wdouglass/pocket-reform/pocket-reform-charger/3d-models/21-0139I_T2444-4_MXM.step

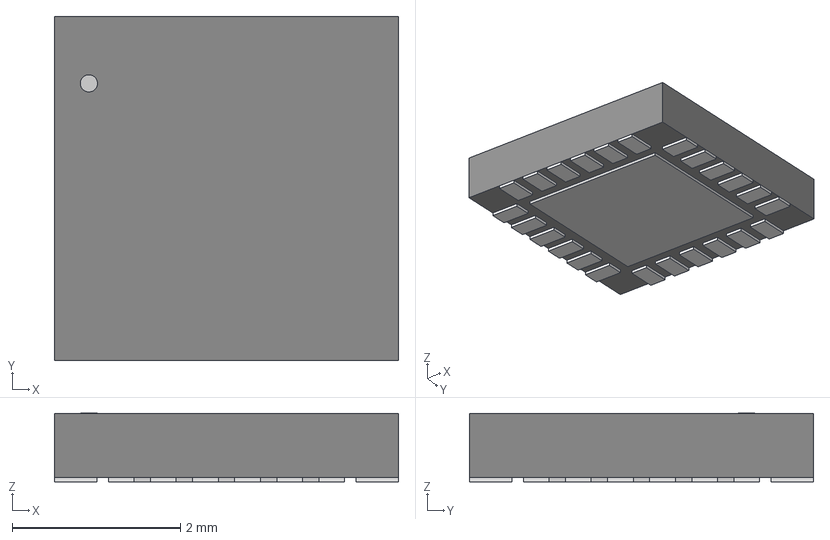
[picture p18: CAD file, 2023-04-12]
pocket-reform-charger/3d-models/21-0139I_T2444-4_MXM.step
4.09 x 4.09 x 0.815 mm
