wdouglass/pocket-reform/pocket-reform-headphones/3d-models/SR42W001.stp

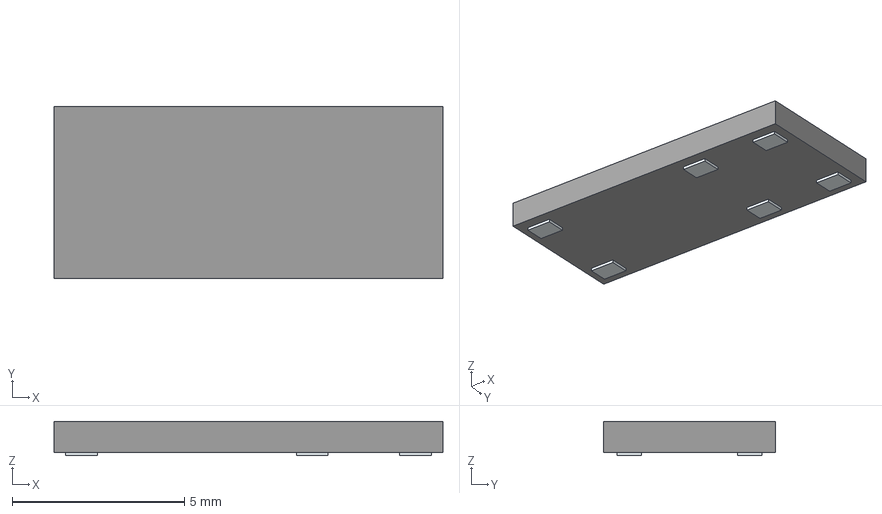
[picture p19: CAD file, 2024-01-16]
pocket-reform-headphones/3d-models/SR42W001.stp
11.3 x 5.00 x 1.00 mm
Pins
