wdouglass/pocket-reform/pocket-reform-motherboard/3d-models/SM02B-SRSS-TB-LF--SN---3DModel-STEP-56544.STEP

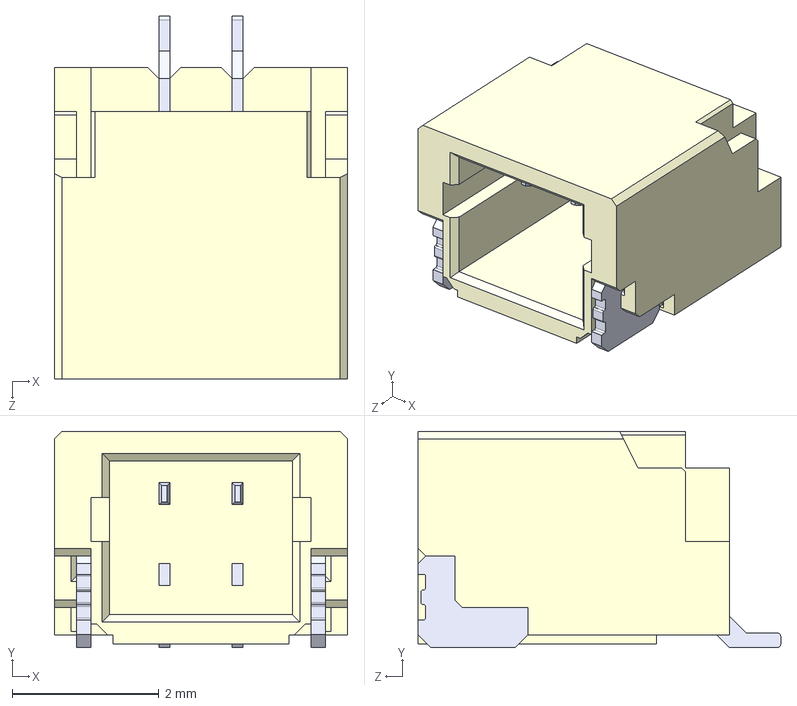
[picture p20: CAD file, 2023-11-24]
pocket-reform-motherboard/3d-models/SM02B-SRSS-TB-LF--SN---3DModel-STEP-56544.STEP
4.00 x 2.95 x 4.95 mm
