wdouglass/pocket-reform/attic/pocket-reform-keyboard/3d-models/Cherry_-_ML1A-11NW.step

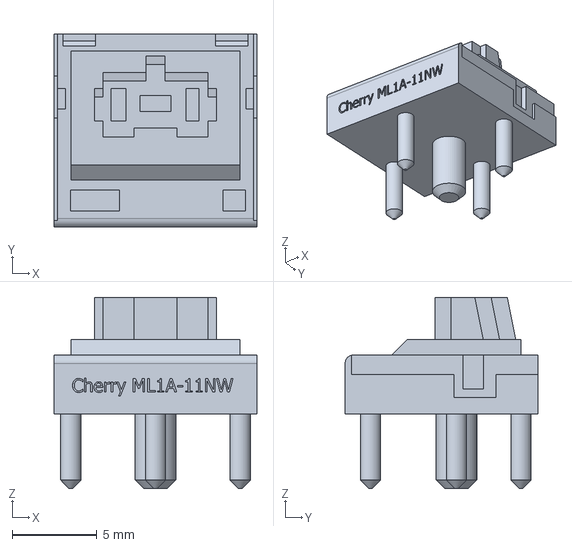
[picture p21: CAD file, 2021-04-30]
attic/pocket-reform-keyboard/3d-models/Cherry_-_ML1A-11NW.step
12.0 x 11.4 x 11.3 mm
