wdouglass/pocket-reform/pocket-reform-charger/3d-models/S9B-PH-SM4-TB.stp

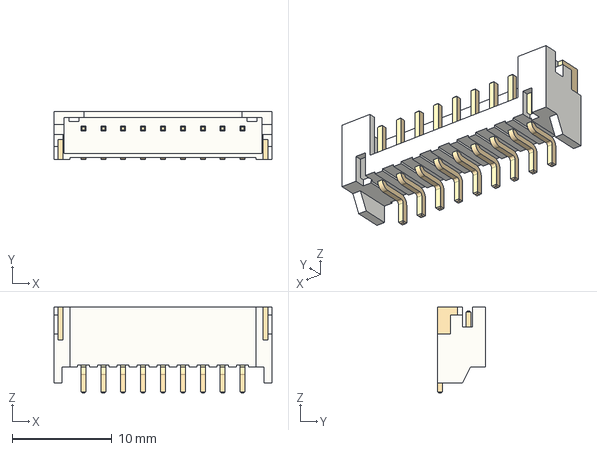
[picture p22: CAD file, 2022-06-08]
pocket-reform-charger/3d-models/S9B-PH-SM4-TB.stp
21.9 x 4.80 x 8.60 mm
