wdouglass/pocket-reform/pocket-reform-headphones/3d-models/SM05B-SRSS-TB(LF)(SN)--3DModel-STEP-418109.STEP

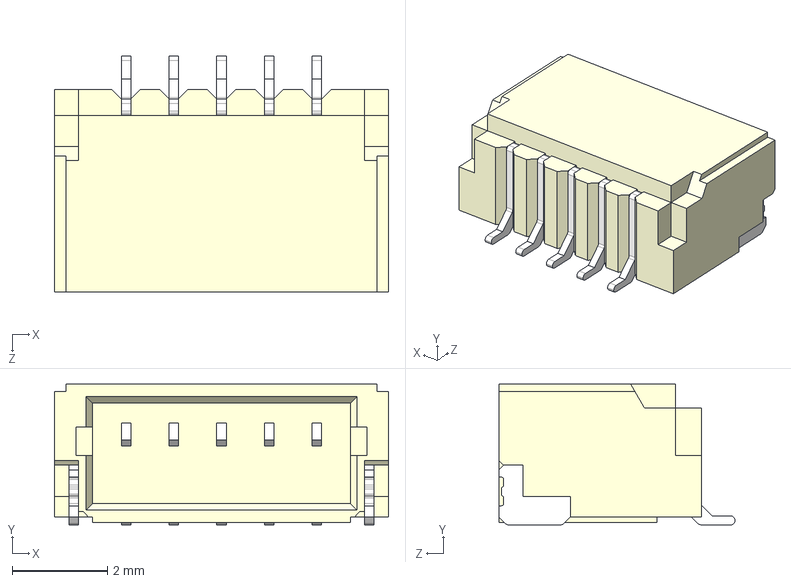
[picture p23: CAD file, 2023-09-29]
pocket-reform-headphones/3d-models/SM05B-SRSS-TB(LF)(SN)--3DModel-STEP-418109.STEP
7.00 x 2.95 x 4.95 mm
