wdouglass/pocket-reform/pocket-reform-headphones/3d-models/CUI_SJ-43516-SMT-TR.step

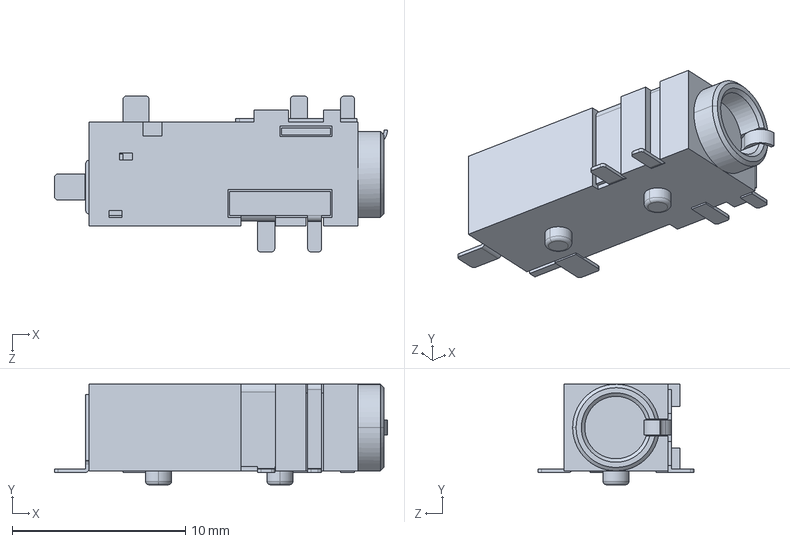
[picture p24: CAD file, 2021-07-28]
pocket-reform-headphones/3d-models/CUI_SJ-43516-SMT-TR.step
19.2 x 5.80 x 9.00 mm
