wdouglass/pocket-reform/pocket-reform-motherboard/3d-models/TSM-103-01-L-DH.step

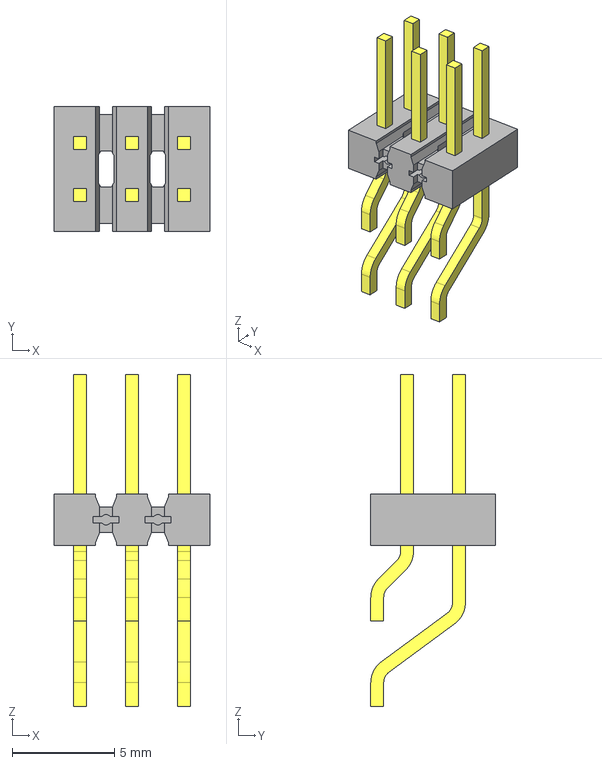
[picture p26: CAD file, 2023-08-25]
pocket-reform-motherboard/3d-models/TSM-103-01-L-DH.step
7.62 x 6.10 x 16.3 mm
T-1S6-09(-01-3-DH)
TSM-103-01-DH_body
