wdouglass/pocket-reform/pocket-reform-motherboard/3d-models/3215-crystal.step

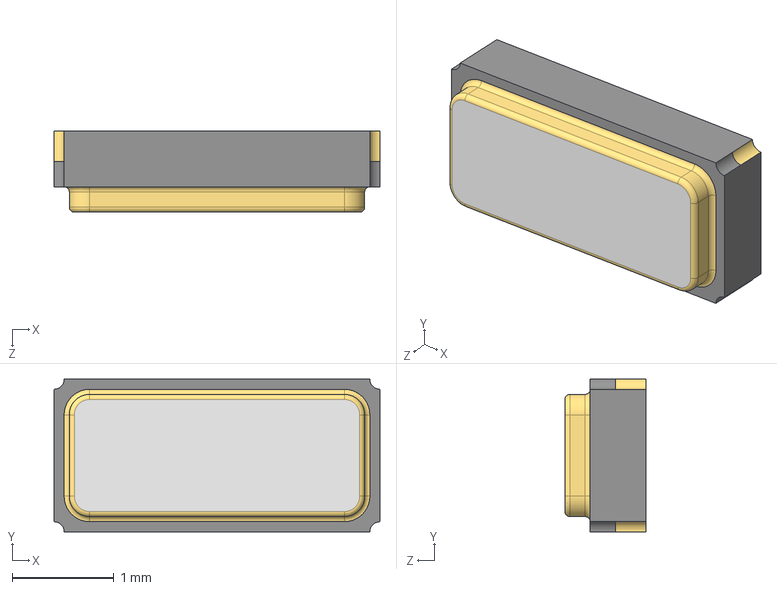
[picture p27: CAD file, 2022-06-17]
pocket-reform-motherboard/3d-models/3215-crystal.step
3.20 x 1.50 x 0.8 mm
