wdouglass/pocket-reform/pocket-reform-motherboard/3d-models/HTQFP-80.stp

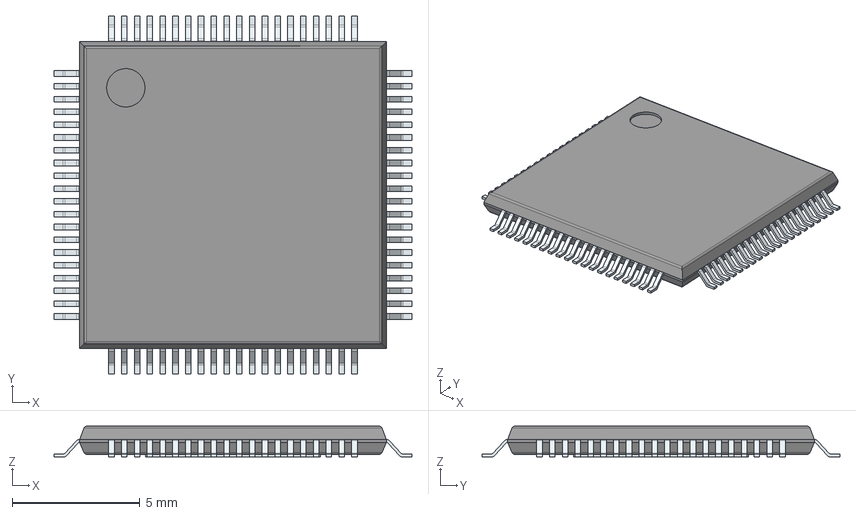
[picture p28: CAD file, 2022-06-17]
pocket-reform-motherboard/3d-models/HTQFP-80.stp
14.0 x 14.0 x 1.20 mm
PinsArrayLR
PinsArrayTB
ThermalPad
