wdouglass/pocket-reform/pocket-reform-motherboard/3d-models/SOD-128.step

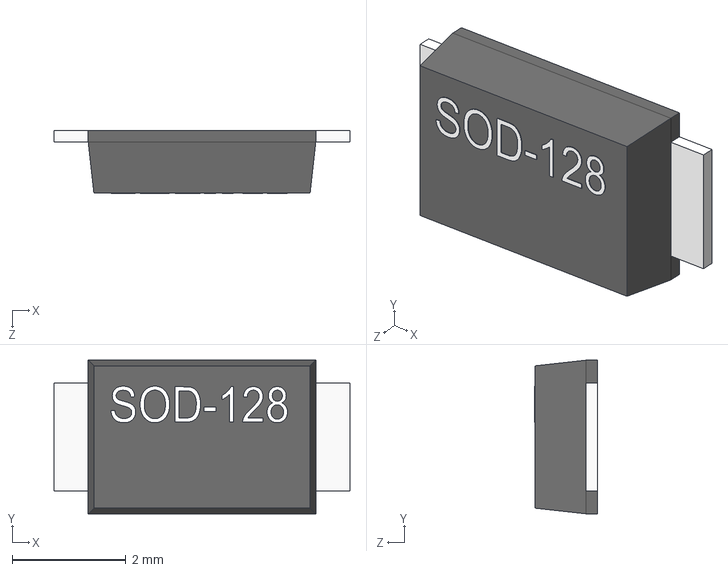
[picture p29: CAD file, 2022-06-17]
pocket-reform-motherboard/3d-models/SOD-128.step
5.20 x 2.70 x 1.11 mm
