wdouglass/pocket-reform/pocket-reform-motherboard/3d-models/IHLP4040DZ (2.2-100uH).STEP

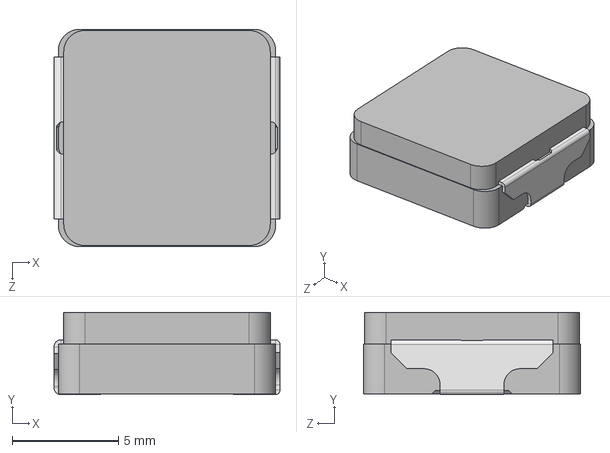
[picture p30: CAD file, 2022-06-08]
pocket-reform-motherboard/3d-models/IHLP4040DZ (2.2-100uH).STEP
10.6 x 3.87 x 10.2 mm
