wdouglass/pocket-reform/pocket-reform-motherboard/3d-models/BK-879.STEP

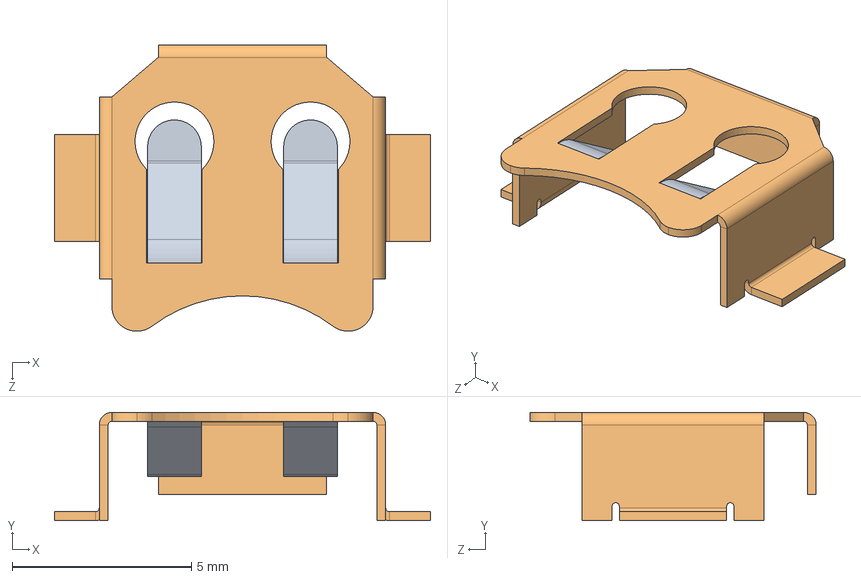
[picture p31: CAD file, 2022-06-08]
pocket-reform-motherboard/3d-models/BK-879.STEP
10.5 x 3.02 x 8.00 mm
