wdouglass/pocket-reform/pocket-reform-motherboard/3d-models/TLV320AIC3100IRHBR.STEP

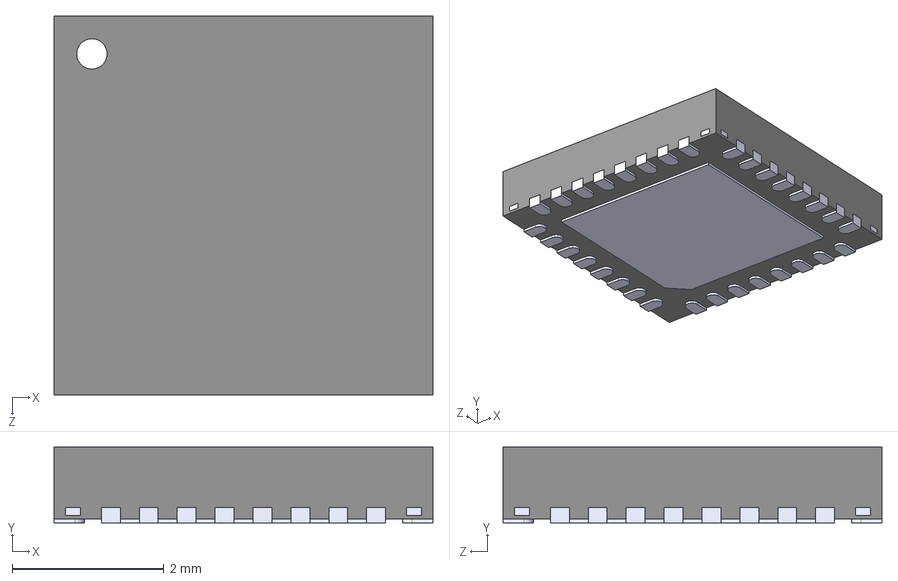
[picture p32: CAD file, 2022-06-08]
pocket-reform-motherboard/3d-models/TLV320AIC3100IRHBR.STEP
5.00 x 1.00 x 5.00 mm
