wdouglass/pocket-reform/pocket-reform-motherboard/3d-models/FH12-33S-0.5SH.stp

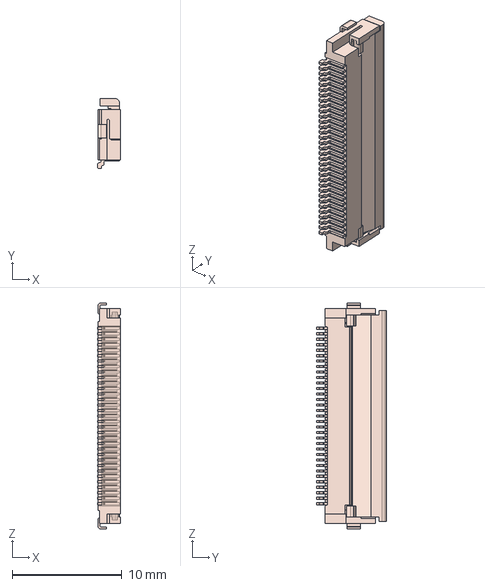
[picture p33: CAD file, 2022-06-08]
pocket-reform-motherboard/3d-models/FH12-33S-0.5SH.stp
2.10 x 6.40 x 20.6 mm
