wdouglass/pocket-reform/pocket-reform-motherboard/3d-models/ssfv33r_1stlf.stp

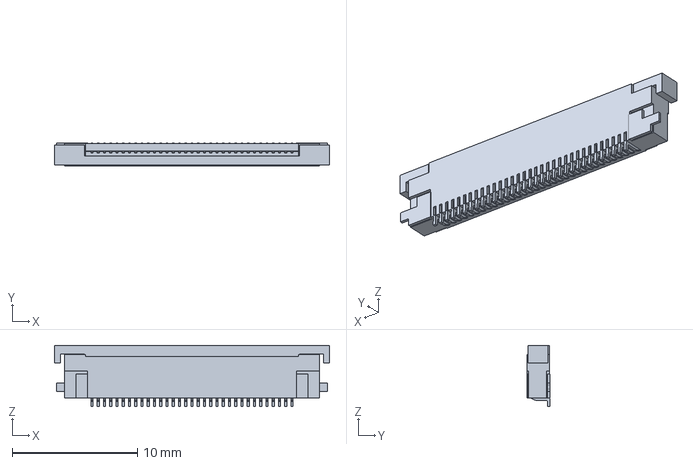
[picture p35: CAD file, 2022-06-08]
pocket-reform-motherboard/3d-models/ssfv33r_1stlf.stp
22.0 x 1.87 x 4.90 mm
