wdouglass/pocket-reform/pocket-reform-motherboard/3d-models/19-337-R6GHBHC-A01-2T.STEP

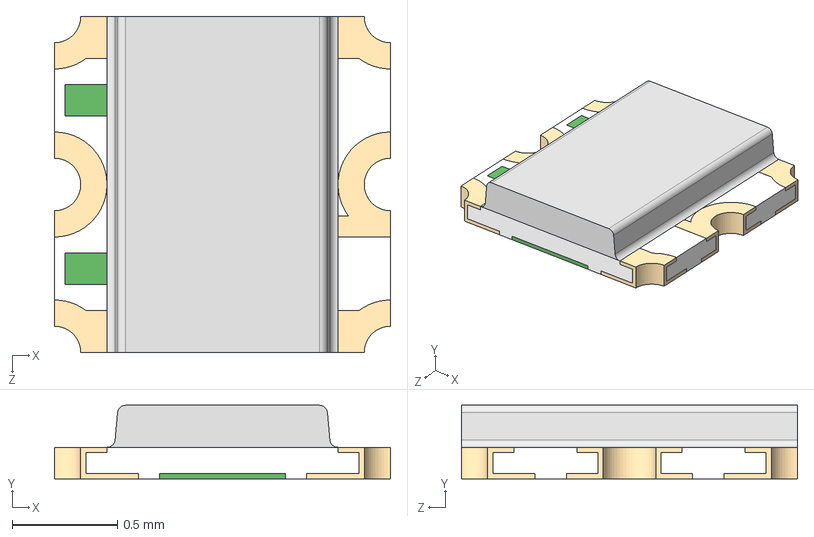
[picture p36: CAD file, 2022-06-08]
pocket-reform-motherboard/3d-models/19-337-R6GHBHC-A01-2T.STEP
1.60 x 0.35 x 1.60 mm
