wdouglass/pocket-reform/pocket-reform-motherboard/3d-models/TYPE-C-31-M-12--3DModel-STEP-56544.STEP

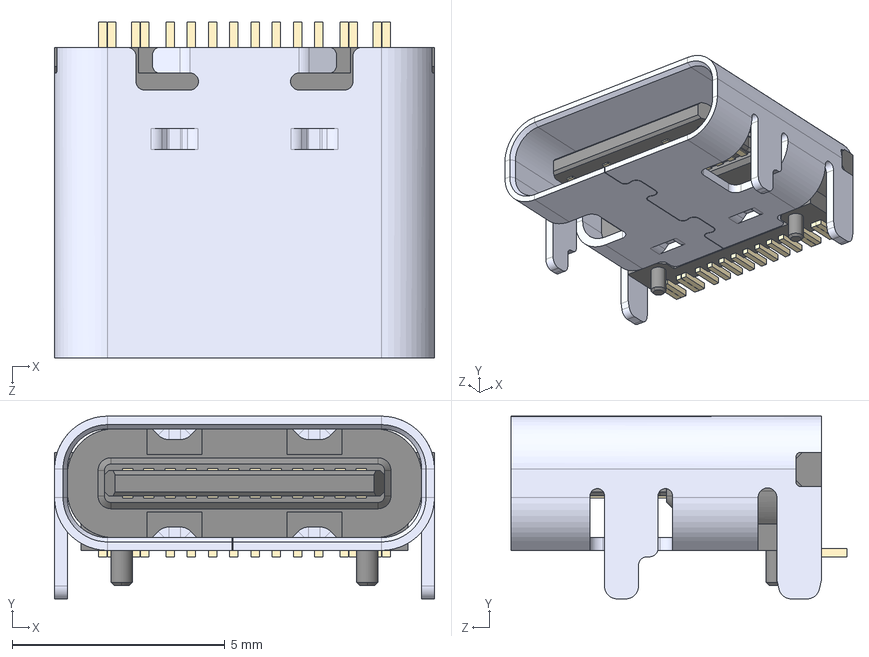
[picture p37: CAD file, 2022-06-08]
pocket-reform-motherboard/3d-models/TYPE-C-31-M-12--3DModel-STEP-56544.STEP
8.94 x 4.30 x 7.90 mm
