wdouglass/pocket-reform/pocket-reform-motherboard/3d-models/IND_TAIYO_NRH3012_TAY.step

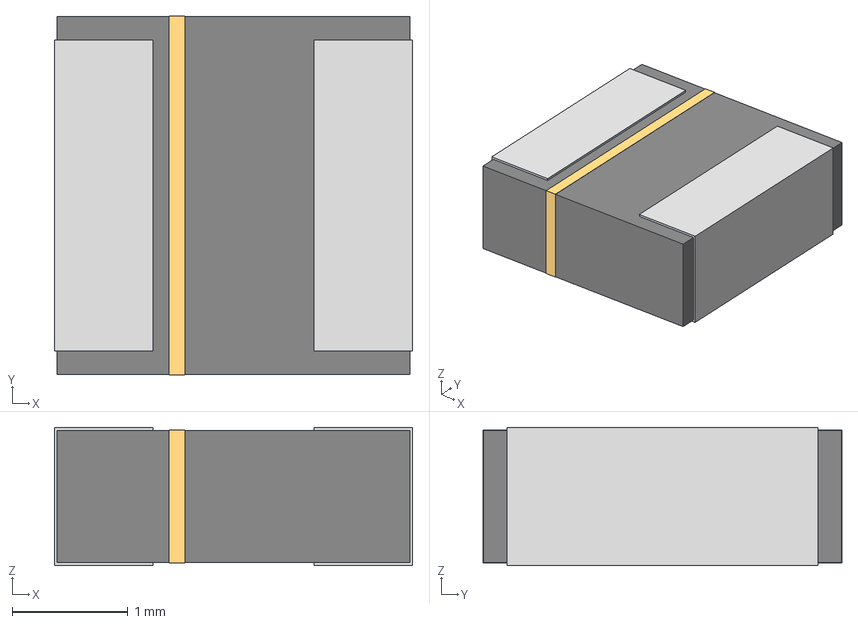
[picture p38: CAD file, 2022-06-08]
pocket-reform-motherboard/3d-models/IND_TAIYO_NRH3012_TAY.step
3.10 x 3.10 x 1.19 mm
