wdouglass/pocket-reform/pocket-reform-motherboard/3d-models/DM3AT-SF-PEJM5--3DModel-STEP-56544.STEP

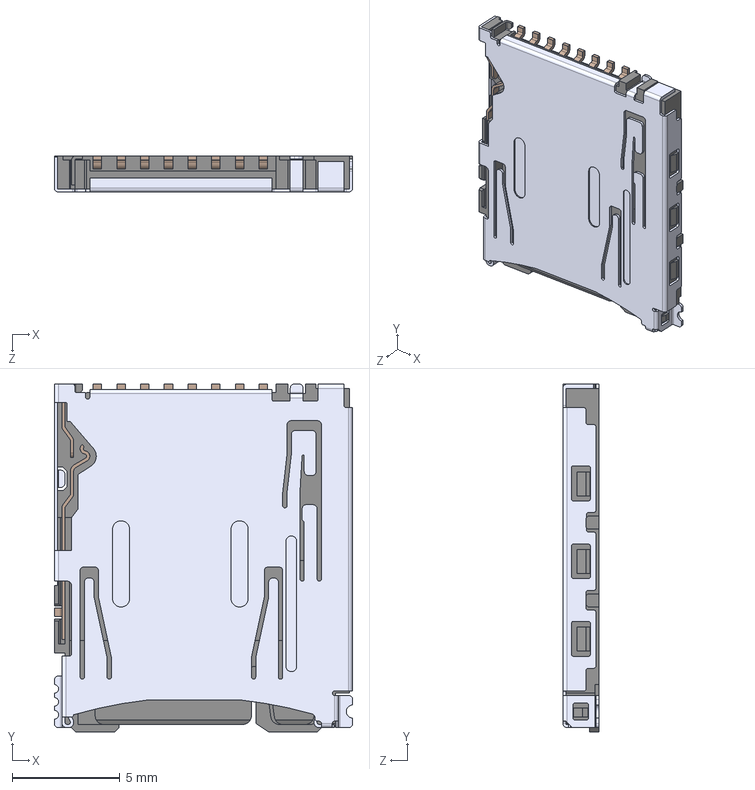
[picture p39: CAD file, 2022-06-08]
pocket-reform-motherboard/3d-models/DM3AT-SF-PEJM5--3DModel-STEP-56544.STEP
13.8 x 16.2 x 1.68 mm
