wdouglass/pocket-reform/pocket-reform-motherboard/3d-models/CM2020-00TR--3DModel-STEP-56544.STEP

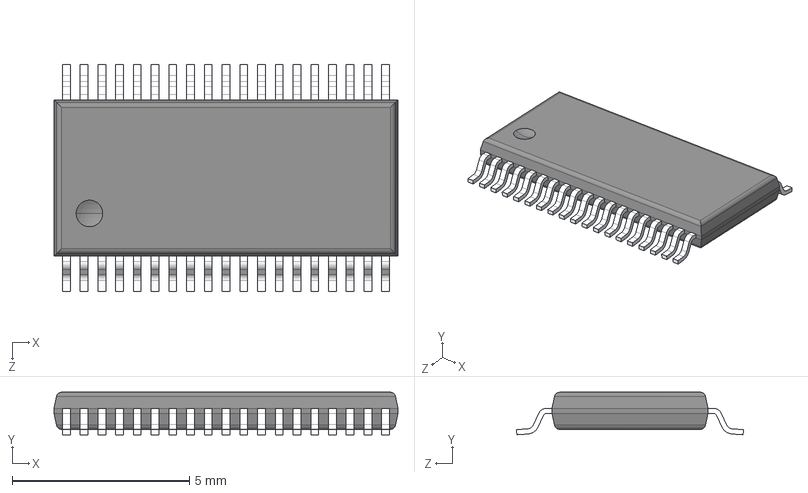
[picture p40: CAD file, 2022-06-08]
pocket-reform-motherboard/3d-models/CM2020-00TR--3DModel-STEP-56544.STEP
9.70 x 1.20 x 6.40 mm
