wdouglass/pocket-reform/pocket-reform-motherboard/3d-models/3-2328724-1.step

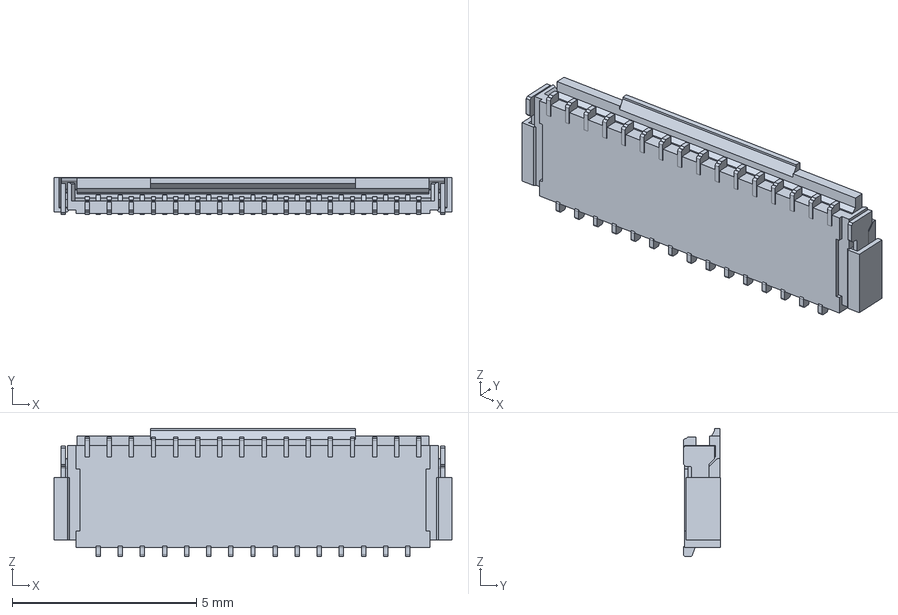
[picture p41: CAD file, 2022-05-31]
pocket-reform-motherboard/3d-models/3-2328724-1.step
10.8 x 1.00 x 3.48 mm
