wdouglass/pocket-reform/pocket-reform-motherboard/3d-models/c-1-2199230-5-b2-3d.stp

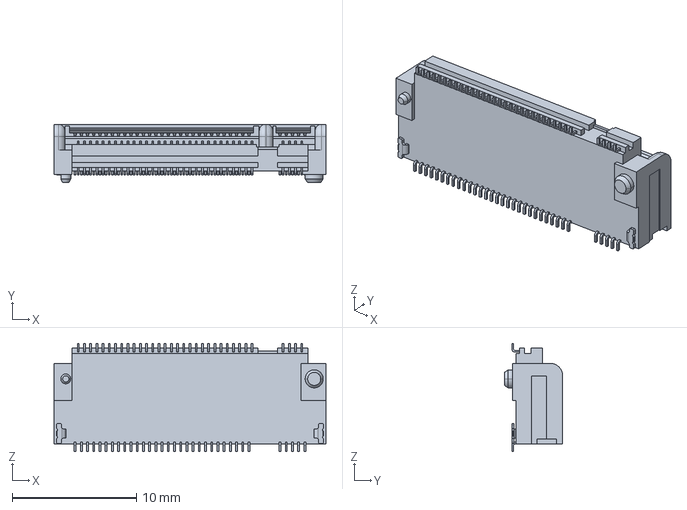
[picture p42: CAD file, 2022-05-31]
pocket-reform-motherboard/3d-models/c-1-2199230-5-b2-3d.stp
21.9 x 4.70 x 8.70 mm
