wdouglass/pocket-reform/pocket-reform-motherboard/3d-models/SON95P300X300X80-7N.step

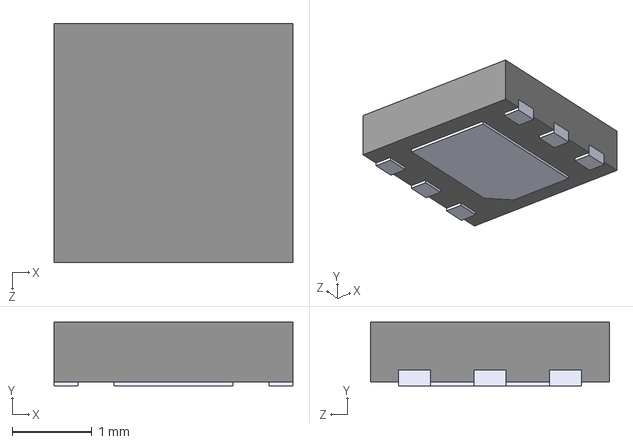
[picture p43: CAD file, 2022-05-31]
pocket-reform-motherboard/3d-models/SON95P300X300X80-7N.step
3.00 x 0.8 x 3.00 mm
