wdouglass/pocket-reform/pocket-reform-motherboard/3d-models/wuerth_692121030100_usb3.stp

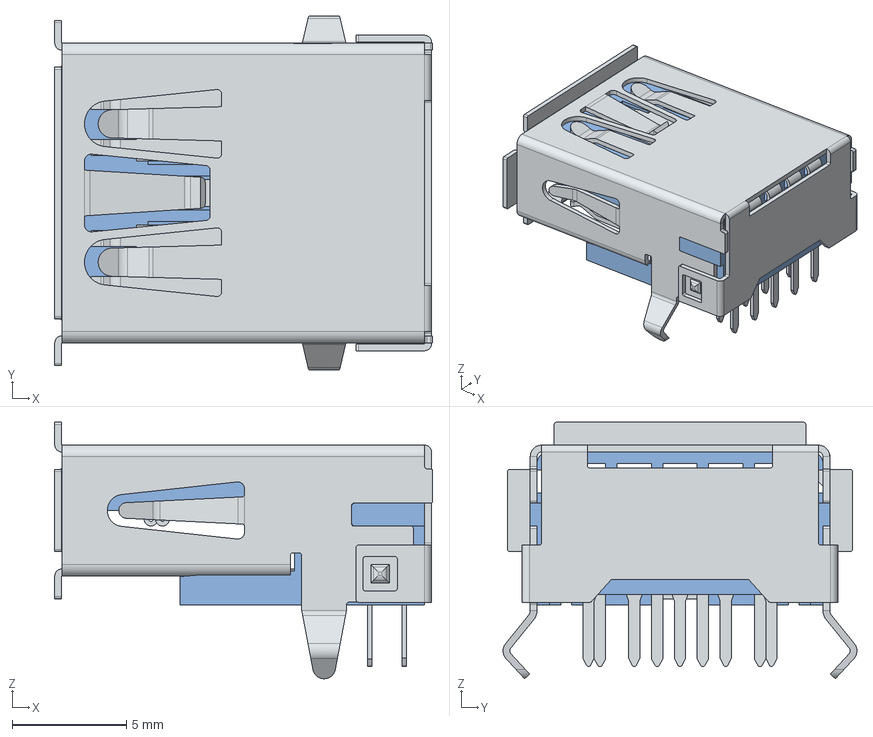
[picture p44: CAD file, 2022-05-31]
pocket-reform-motherboard/3d-models/wuerth_692121030100_usb3.stp
16.6 x 15.5 x 11.2 mm
housing1
pin1 x 5
housing2
pin2 x 2
pin x 2
shielding
