wdouglass/pocket-reform/pocket-reform-motherboard/3d-models/p36-2.stp

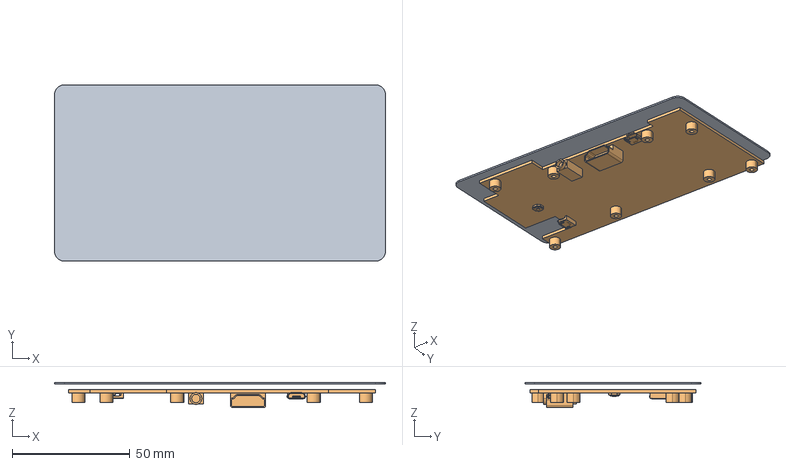
[picture p45: CAD file, 2021-07-28]
pocket-reform-motherboard/3d-models/p36-2.stp
140.4 x 74.8 x 10.8 mm
