wdouglass/pocket-reform/pocket-reform-motherboard/3d-models/Bateria 18650 3.7 V 1300 mAh d.18 mm.STEP

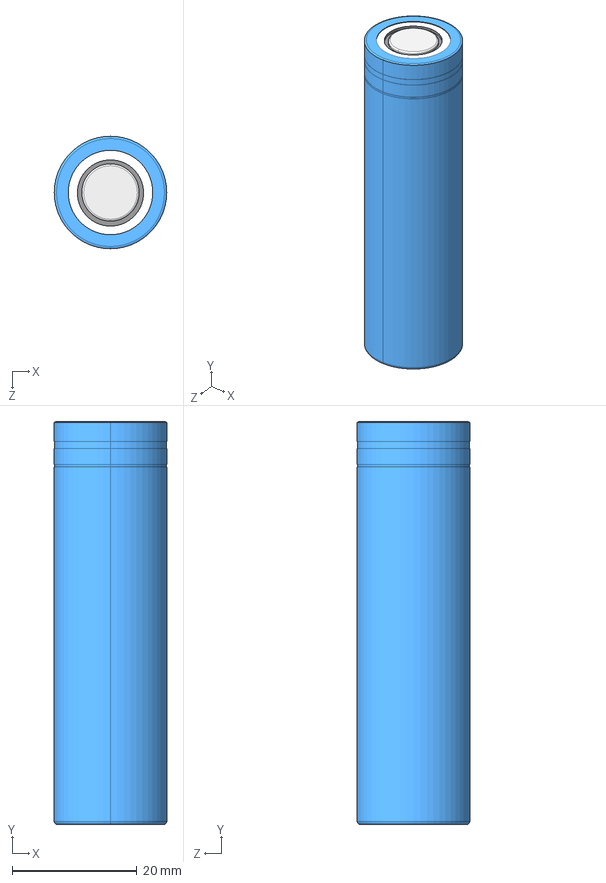
[picture p46: CAD file, 2021-07-28]
pocket-reform-motherboard/3d-models/Bateria 18650 3.7 V 1300 mAh d.18 mm.STEP
18.1 x 64.7 x 18.1 mm
