wdouglass/pocket-reform/pocket-reform-motherboard/3d-models/DM3CS-SFb.stp

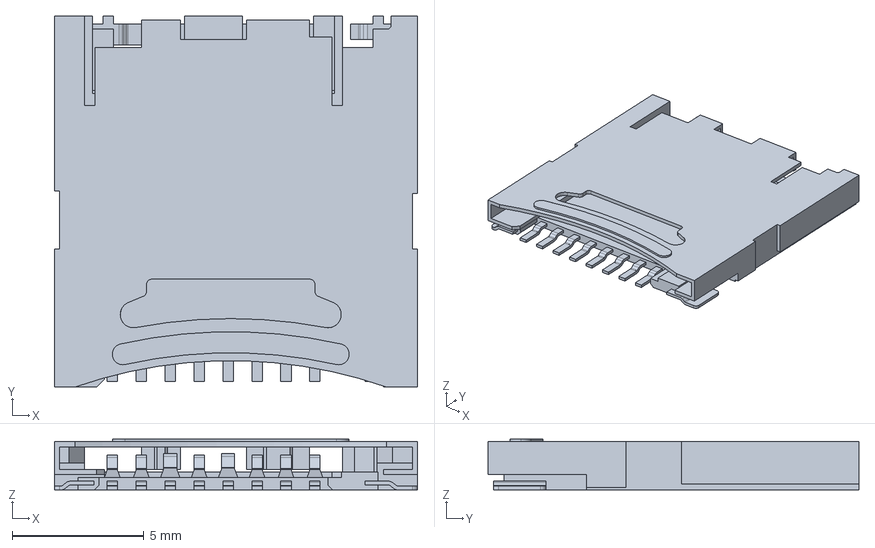
[picture p47: CAD file, 2021-07-28]
pocket-reform-motherboard/3d-models/DM3CS-SFb.stp
13.8 x 14.1 x 1.93 mm
