wdouglass/pocket-reform/pocket-reform-motherboard/3d-models/keystone-PN54.STEP

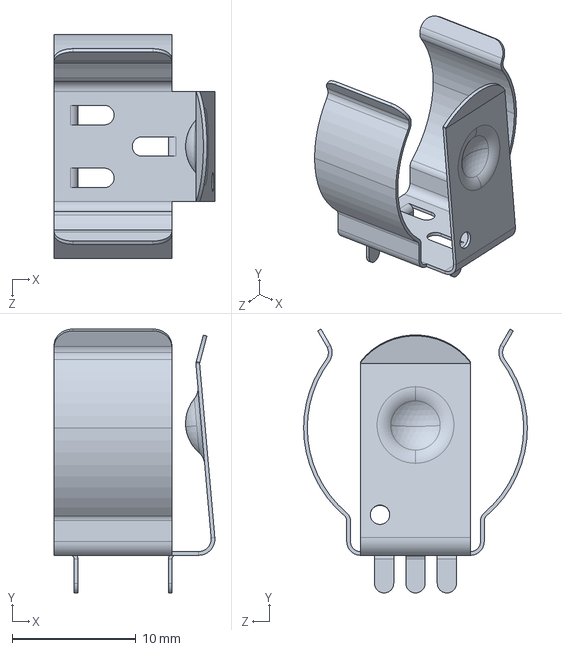
[picture p48: CAD file, 2021-07-28]
pocket-reform-motherboard/3d-models/keystone-PN54.STEP
13.0 x 21.4 x 18.1 mm
