wdouglass/pocket-reform/pocket-reform-motherboard/3d-models/c-2199337-5-a-3d.stp

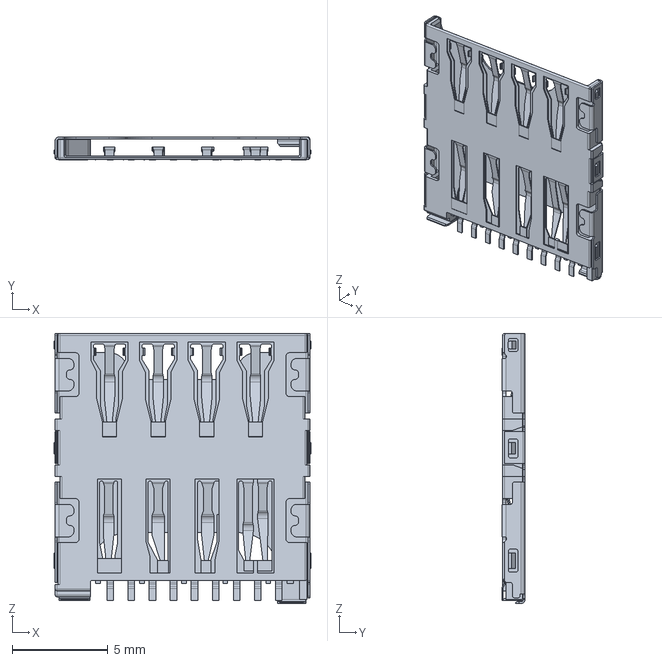
[picture p49: CAD file, 2021-07-28]
pocket-reform-motherboard/3d-models/c-2199337-5-a-3d.stp
13.4 x 1.20 x 14.1 mm
