wdouglass/pocket-reform/pocket-reform-keyboard-fw/pocket-hid/src/remote.h

/*
  SPDX-License-Identifier: GPL-3.0-or-later
  MNT Pocket Reform Keyboard/Trackball Controller Firmware for RP2040
  Copyright 2021-2024 MNT Research GmbH (mntre.com)
*/

#ifndef _REMOTE_H_
#define _REMOTE_H_

void insert_bat_icon(char* str, int x, double v);
void empty_serial(void);
int remote_receive_string(int print);
int remote_try_wakeup(void);
int remote_try_command(const char* cmd, int print_response);
int remote_get_voltages(int quiet);
int remote_check_for_low_battery(void);
int remote_get_status(void);
int remote_turn_on_som(void);
int remote_turn_off_som(void);
int remote_reset_som(void);
int remote_wake_som(void);
int remote_report_voltages(void);
int remote_enable_som_uart(void);
int remote_disable_som_uart(void);
void remote_process_alerts(void);
void remote_init(void);
void remote_on_uart_rx(void);
int remote_get_power_state(void);

#endif
